epccs/RPUftdi/Hardware/Design/MultiDrop.sch

## EAGLE design Hardware/Design/MultiDrop.sch (2017-11-28)

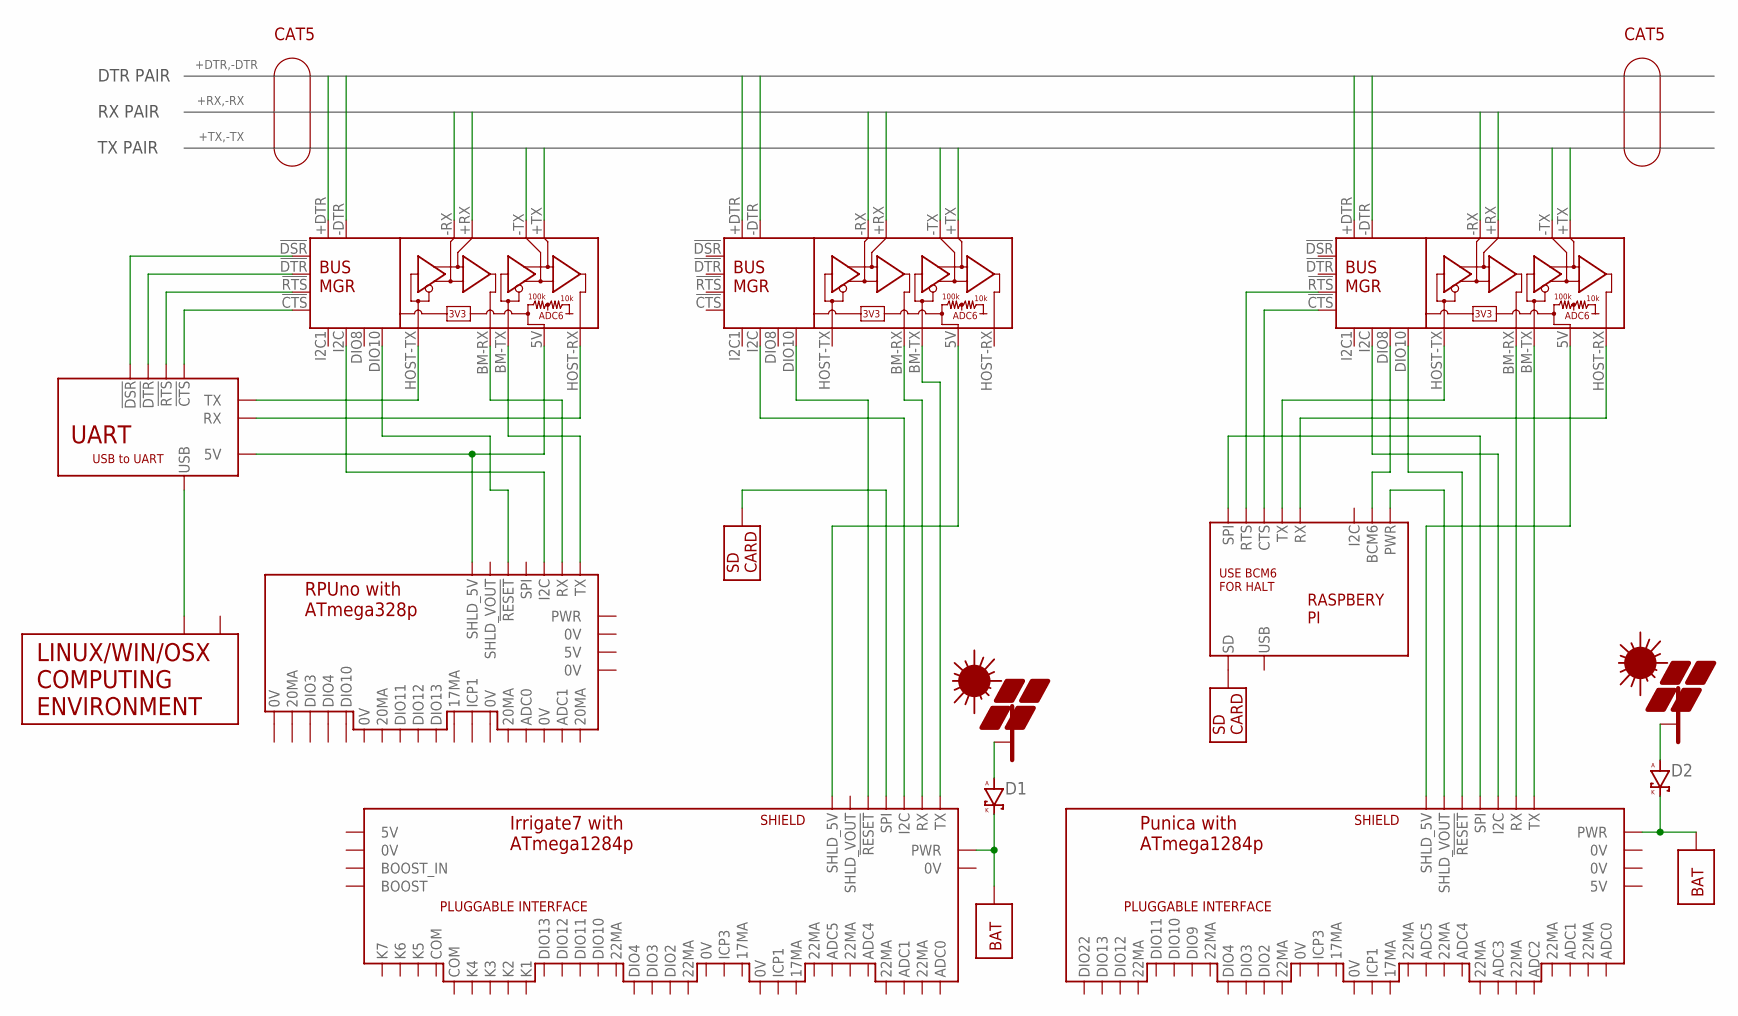
[picture p20: schematic MultiDrop.sch]

Parts:
BM2: RPUNO; NA-30
D1, D2: DSMB; SMB
PM1: DESKTOP; NA-30
PV2, PV4: PV; NA-30
SD1, SD2: SD; NA-30
U$1, U$2, U$4: BUS_MGR; WITH_RPU_NAMES
U$3: PI; NA-30
U$5: IRRIGATE7; WITH_RPU_NAMES
U$7, U$9: BAT; NA-30
U$8: PUNICA; WITH_RPU_NAMES
UART1: UART; NA-30

Connections:
+DTR: U$4.+DTR
+DTR1: U$2.+DTR
+DTR3: U$1.+DTR
+RX: U$4.+RX
+RX1: U$2.+RX
+RX3: U$1.+RX
+TX: U$4.+TX
+TX1: U$2.+TX
+TX3: U$1.+TX
-DTR: U$4.-DTR
-DTR1: U$2.-DTR
-DTR3: U$1.-DTR
-RX: U$4.-RX
-RX1: U$2.-RX
-RX3: U$1.-RX
-TX: U$4.-TX
-TX1: U$2.-TX
-TX3: U$1.-TX
unnamed: BM2.1 (TX), U$4.BM-TX (BM_TX)
unnamed: BM2.2 (RX), U$4.BM-RX (BM_RX)
unnamed: PM1.1 (RX), UART1.7 (USB)
unnamed: U$4.!CTS, UART1.1 (!CTS)
unnamed: U$4.!RTS, UART1.4 (!RTS)
unnamed: U$4.!DTR, UART1.3 (!DTR)
unnamed: U$4.!DSR, UART1.2 (!DSR)
unnamed: U$4.HOST-RX (HOST_RX), UART1.5 (RX)
unnamed: U$4.HOST-TX (HOST_TX), UART1.6 (TX)
unnamed: U$2.BM-TX (BM_TX), U$5.TX
unnamed: U$2.BM-RX (BM_RX), U$5.RX
unnamed: U$1.DIO8, U$3.7 (BCM6)
unnamed: U$1.5V (PWR), U$8.SHLD_5V
unnamed: U$1.BM-TX (BM_TX), U$8.TX
unnamed: D2.K, U$7.1, U$8.PWR
unnamed: D2.A, PV4.1
unnamed: D1.A, PV2.1
unnamed: D1.K, U$5.PWR, U$9.1
unnamed: SD1.1, U$5.SPI
unnamed: U$1.BM-RX (BM_RX), U$8.RX
unnamed: U$1.!CTS, U$3.1 (CTS)
unnamed: U$1.!RTS, U$3.2 (RTS)
unnamed: U$3.10 (SPI), U$8.SPI
unnamed: U$1.HOST-RX (HOST_RX), U$3.3 (RX)
unnamed: U$1.HOST-TX (HOST_TX), U$3.4 (TX)
unnamed: SD2.1, U$3.9 (SD)
unnamed: BM2.6 (SHLD_5V), U$4.5V (PWR), UART1.8 (5V)
unnamed: BM2.5 (!RESET), U$4.DIO10
unnamed: U$1.I2C, U$8.I2C
unnamed: BM2.3 (I2C), U$4.I2C
unnamed: U$3.12 (PWR), U$8.SHLD_VOUT
unnamed: U$1.DIO10, U$8.!RESET
unnamed: U$2.DIO10, U$5.!RESET
unnamed: U$2.5V (PWR), U$5.SHLD_5V
unnamed: U$2.I2C, U$5.I2C

Notes on the sheet:
CAT5
DTR PAIR
RX PAIR
TX PAIR
